zhbi98/PowerWatch/Firmware/test/src/ina226/ina226.c

/**
 * @file ina226.c
 *
 */

#include "ina226.h"

/**********************
 *      TYPEDEFS
 **********************/

INA226_Data_Typedef INA226_Data;

/**********************
 * STATIC PROTOTYPES
 **********************/

static void INA226_SetRegPointer(uint8_t addr,uint8_t reg);
static void INA226_SendData(uint8_t addr, uint8_t reg, uint16_t data);
static uint16_t INA226_ReadData(uint8_t addr);
static void INA226_Get_ID(uint8_t addr);              /**< 获取 ID*/
static void INA226_Get_MID(uint8_t addr);             /**< 获取 Manufacturer ID*/
static uint16_t INA226_Get_CAL_Reg(uint8_t addr);     /**< 获取校准值*/
static uint16_t INA226_GetVoltage( uint8_t addr);     /**< 获取总线电压装载值*/
static int16_t INA226_GetShuntCurrent(uint8_t addr);  /**< 获取分流电流装载值*/
static int16_t INA226_GetShuntVoltage(uint8_t addr);  /**< 分流电压装载值*/
static uint16_t INA226_GetPower(uint8_t addr);        /**< 获取功率装载值，不使用*/

/**********************
 * GLOBAL FUNCTIONS
 **********************/

/*初始化 I2C 和 INA226 寄存器*/
void INA226_Init(void)
{
    /*IIC_Init();*/
    ina226_gpio_init();
    INA226_SendData(INA226_ADDR1, CFG_REG, 0x8000); /*重新启动*/
    INA226_SendData(INA226_ADDR1, CFG_REG, MODE_INA226);
    INA226_SendData(INA226_ADDR1, CAL_REG, CAL); /*设置分辨率*/
    INA226_Get_ID(INA226_ADDR1); /*获取 INA226 的 ID*/
    INA226_Get_MID(INA226_ADDR1);
}

/*发送, 写入数据*/
void INA226_SendData(uint8_t addr, uint8_t reg, uint16_t data)
{
    uint8_t temp = 0;
    ina226_i2c_start(); /*IIC_Start();*/

    ina226_i2c_send_byte(addr); /*IIC_Send_Byte(addr);*/
    ina226_i2c_wait_ack(); /*IIC_Wait_Ack();*/

    ina226_i2c_send_byte(reg); /*IIC_Send_Byte(reg);*/
    ina226_i2c_wait_ack(); /*IIC_Wait_Ack();*/
    
    temp = (uint8_t)(data >> 8);
    ina226_i2c_send_byte(temp); /*IIC_Send_Byte(temp);*/
    ina226_i2c_wait_ack(); /*IIC_Wait_Ack();*/

    temp = (uint8_t)(data & 0x00ff);
    ina226_i2c_send_byte(temp); /*IIC_Send_Byte(temp);*/
    ina226_i2c_wait_ack(); /*IIC_Wait_Ack();*/
    
    ina226_i2c_stop(); /*IIC_Stop();*/
}

/*设置寄存器指针*/
void INA226_SetRegPointer(uint8_t addr, uint8_t reg)
{
    ina226_i2c_start(); /*IIC_Start();*/

    ina226_i2c_send_byte(addr); /*IIC_Send_Byte(addr);*/
    ina226_i2c_wait_ack(); /*IIC_Wait_Ack();*/

    ina226_i2c_send_byte(reg); /*IIC_Send_Byte(reg);*/
    ina226_i2c_wait_ack(); /*IIC_Wait_Ack();*/

    ina226_i2c_stop(); /*IIC_Stop();*/
}

/*读取数据*/
uint16_t INA226_ReadData(uint8_t addr)
{
    uint16_t temp=0;
    ina226_i2c_start(); /*IIC_Start();*/

    ina226_i2c_send_byte(addr + 1); /*IIC_Send_Byte(addr+1);*/
    ina226_i2c_wait_ack(); /*IIC_Wait_Ack();*/
    
    temp = ina226_i2c_read_byte(1); /*IIC_Read_Byte(1);*/
    temp <<= 8;   
    temp |= ina226_i2c_read_byte(0); /*IIC_Read_Byte(0);*/
    
    ina226_i2c_stop(); /*IIC_Stop();*/
    return temp;
}

/*获取 ID*/
void INA226_Get_ID(uint8_t addr)
{
    uint32_t temp = 0;
    INA226_SetRegPointer(addr, INA226_GET_ADDR);
    temp = INA226_ReadData(addr);
    INA226_Data.ID = temp;
}

/*获取 Manufacturer ID*/
void INA226_Get_MID(uint8_t addr)
{
    uint32_t temp = 0;
    INA226_SetRegPointer(addr, INA226_GET_MID);
    temp = INA226_ReadData(addr);
    INA226_Data.MID = temp;
}

/*获取校准值*/
uint16_t INA226_Get_CAL_Reg(uint8_t addr)
{
    uint32_t temp = 0;
    INA226_SetRegPointer(addr, CAL_REG);
    temp = INA226_ReadData(addr);
    return (uint16_t)temp;
}

/*总线电压寄存器02H----------->1.25mV/bit (LSB 1.25mV)*/
uint16_t INA226_GetVoltage(uint8_t addr)
{
    uint32_t temp = 0;
    INA226_SetRegPointer(addr, BV_REG);
    temp = INA226_ReadData(addr);
    return (uint16_t)temp;
}

/*分流电压寄存器01H----------->2.5uV/bit (LSB 2.5uV)*/
int16_t INA226_GetShuntVoltage(uint8_t addr)
{
    int16_t temp = 0;
    INA226_SetRegPointer(addr, SV_REG);
    temp = INA226_ReadData(addr);
    /*if (temp&0x8000) temp = ~(temp - 1);*/
    return (int16_t)temp;
}

/*电流寄存器04H----------->0.1mA/bit（这需要根据电流采样电阻的阻值来确定）*/
int16_t INA226_GetShuntCurrent(uint8_t addr)
{
    int16_t temp=0;
    INA226_SetRegPointer(addr, CUR_REG);
    temp = INA226_ReadData(addr);
    /*if (temp & 0x8000) temp = ~(temp - 1);*/
    return temp;
}

/*功率寄存器03H----------->25.0*CURRENT_LSB mW/bit (LSB 25.0*CURRENT_LSBmW)*/
uint16_t INA226_GetPower(uint8_t addr)
{
    int16_t temp=0;
    INA226_SetRegPointer(addr, PWR_REG);
    temp = INA226_ReadData(addr);
    return (uint16_t)temp;
}

/*获取总线电压----------->1.25mV/bit*/
void Get_Bus_Voltage(float * Voltage) /*mV*/
{
    /*LSB 为 1.25 mV*/
    *Voltage = INA226_GetVoltage(INA226_ADDR1) * VOLTAGE_LSB;
}

/*获取分流电压----------->2.5uV/bit*/
void Get_Shunt_voltage(float * Voltage) /*uV*/
{
    /*LSB 为 2.5 uV*/
    *Voltage = (INA226_GetShuntVoltage(INA226_ADDR1) * INA226_VAL_LSB); /*如需矫正电流分流参数请将这里改为 2.5*/
}

/*获取电流----------->0.1mA/bit*/
void Get_Shunt_Current(float * Current) /*mA*/
{
    /*LSB 为 0.1 mA*/
    *Current = (INA226_GetShuntCurrent(INA226_ADDR1) * CURRENT_LSB);
}

/*获取功率----------->25.0*CURRENT_LSBmW/bit*/
void Get_Power(float * Power) /*mW*/
{
    /*LSB 为 25.0*CURRENT_LSB mW*/
    *Power = (INA226_GetPower(INA226_ADDR1) * POWER_LSB);
}

/*获取总线电压，分压，电流，功率，计算功率*/
void INA226_Update()
{
    Get_Bus_Voltage(&INA226_Data.Bus_voltage);      /*mV*/
    Get_Shunt_voltage(&INA226_Data.Shunt_voltage);  /*uV*/
    Get_Shunt_Current(&INA226_Data.Shunt_Current);  /*mA*/
    Get_Power(&INA226_Data.Power);                  /*mW*/

    /*获取功率 = 总线电压 * 电流，
    其中 1mW 等于 1V * 1mA 或 1mV * 1A*/
    INA226_Data.Ref_Power = (INA226_Data.Bus_voltage 
        * 0.001f) * (INA226_Data.Shunt_Current * 1.0f);/*mW*/
}

/*设置报警*/
uint8_t INA226_AlertAddr()
{
    uint8_t temp;
    ina226_i2c_start(); /*IIC_Start();*/

    ina226_i2c_send_byte(INA226_GETALADDR); /*IIC_Send_Byte(INA226_GETALADDR);*/
    ina226_i2c_wait_ack(); /*IIC_Wait_Ack();*/

    temp = ina226_i2c_read_byte(1); /*IIC_Read_Byte(1);*/

    ina226_i2c_stop(); /*IIC_Stop();*/
    return temp;
}
