zhbi98/PowerWatch/Firmware/test/src/UIPages/Recent/recent.h

/**
 * @file sheet.h
 *
 */

#ifndef __RECENT_H__
#define __RECENT_H__

/*********************
 *      INCLUDES
 *********************/

#include <stdlib.h>
#include "strifica.h"
#include "recentview.h"
#include "nt_pm.h"

/*********************
 *      DEFINES
 *********************/

/**********************
 *      TYPEDEFS
 **********************/

/**********************
 * GLOBAL PROTOTYPES
 **********************/

extern const nt_view_t recentview;

#endif /*__SHEET_H__*/
